lou12de39r/ashiyu/docs/stand_5deg.png

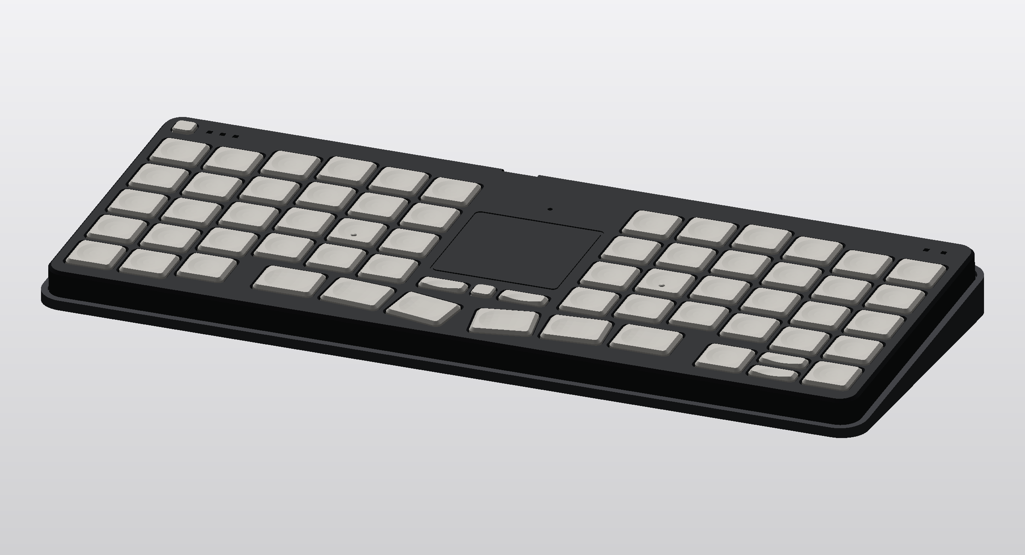
docs/stand_5deg.png
