lou12de39r/ashiyu/docs/case_black_top.png

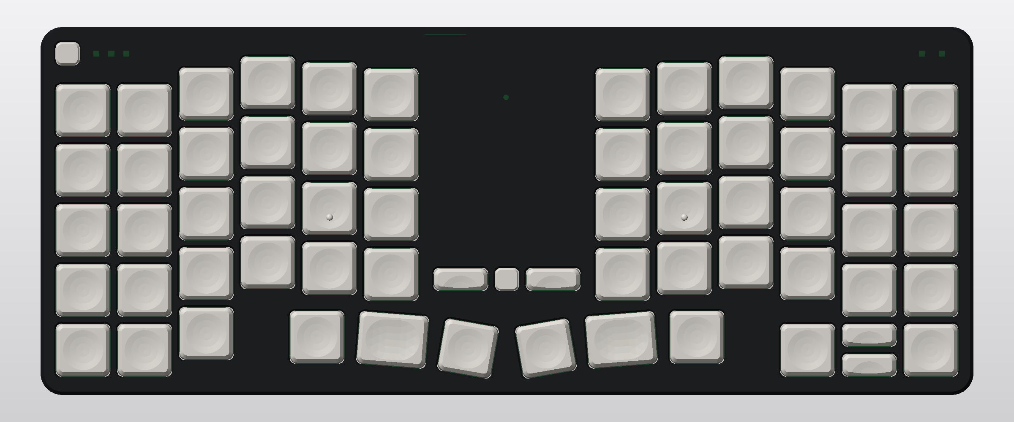
docs/case_black_top.png
