lou12de39r/ashiyu/docs/case_black_white_caps.png

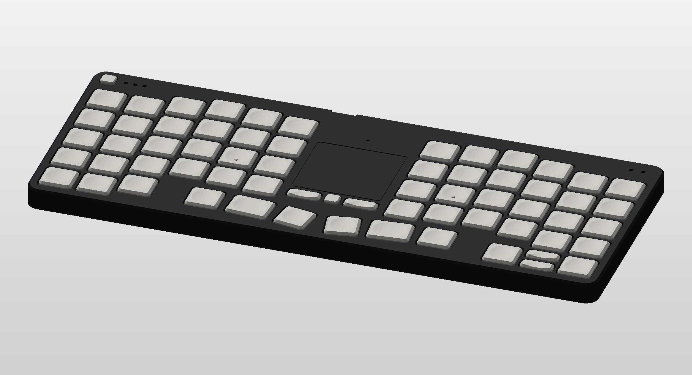
docs/case_black_white_caps.png
