lou12de39r/ashiyu/docs/case_bottom_plate.png

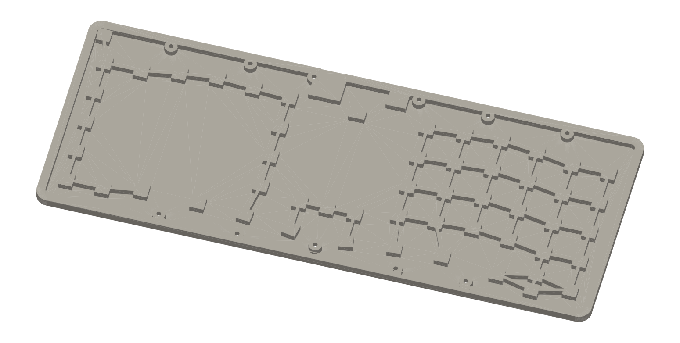
docs/case_bottom_plate.png
