lou12de39r/ashiyu/docs/case_keyhole_corners.png

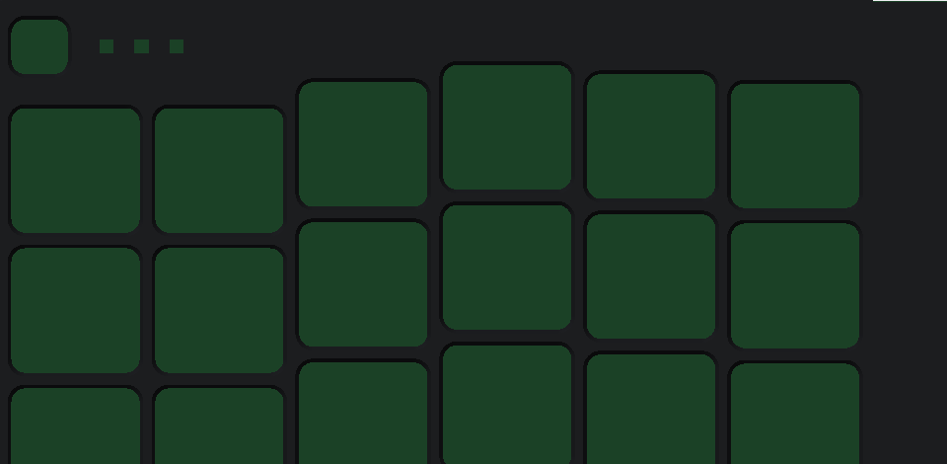
docs/case_keyhole_corners.png
