lou12de39r/ashiyu/docs/case_section_G.png

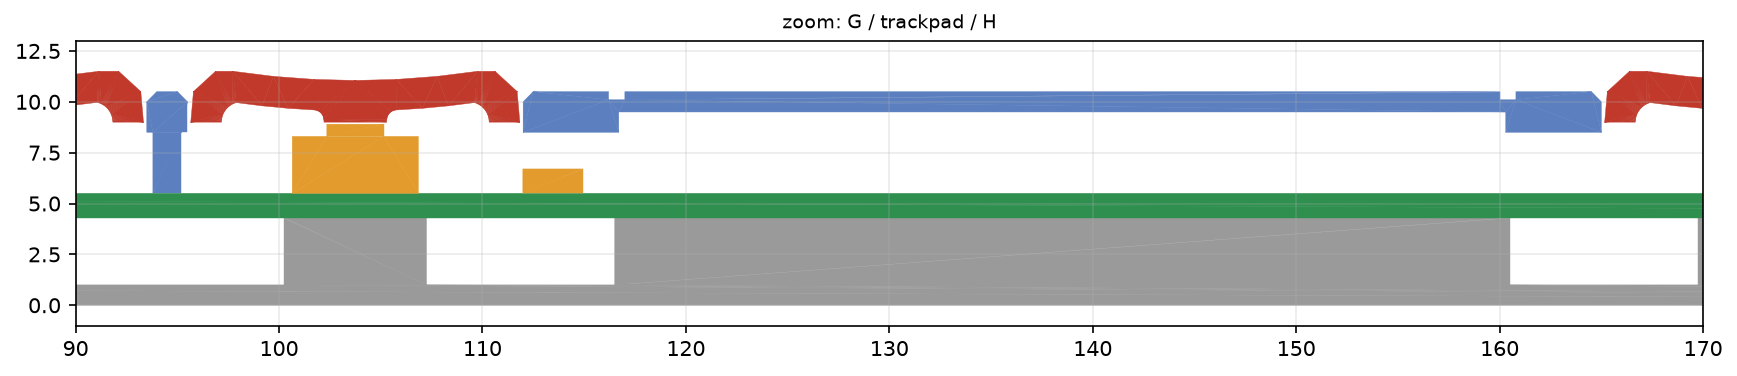
docs/case_section_G.png
