lou12de39r/ashiyu/docs/case_top.png

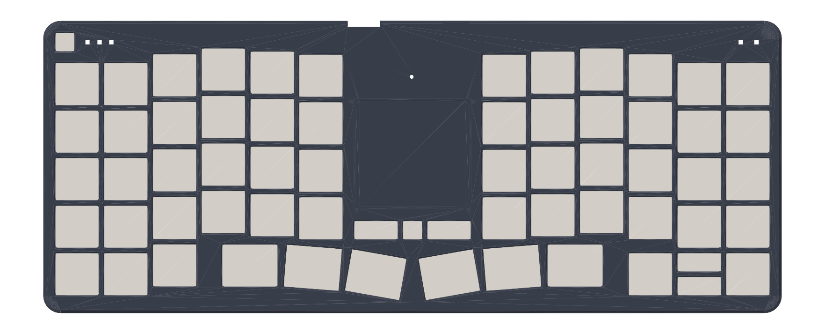
docs/case_top.png
