lou12de39r/ashiyu/docs/exterior_oblique.png

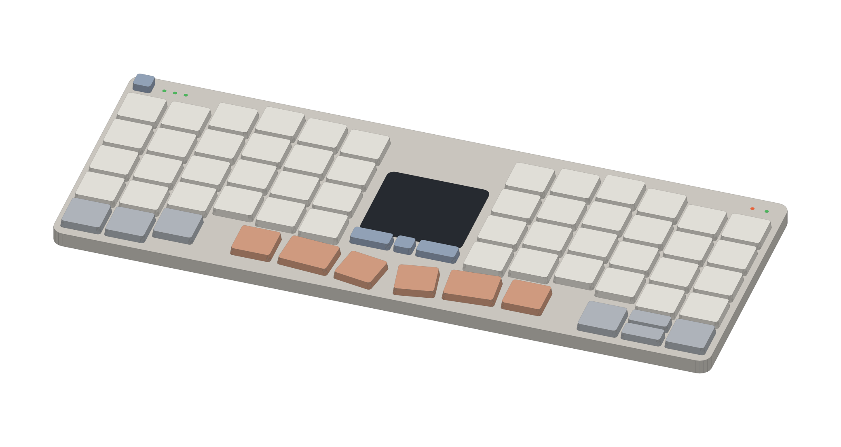
docs/exterior_oblique.png
