lou12de39r/ashiyu/docs/exterior_top.png

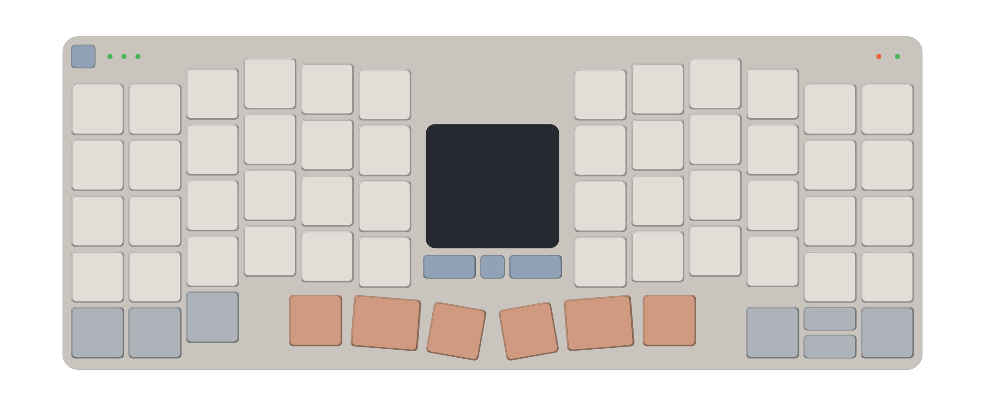
docs/exterior_top.png
