lou12de39r/ashiyu/docs/layout_splay6_compare.png

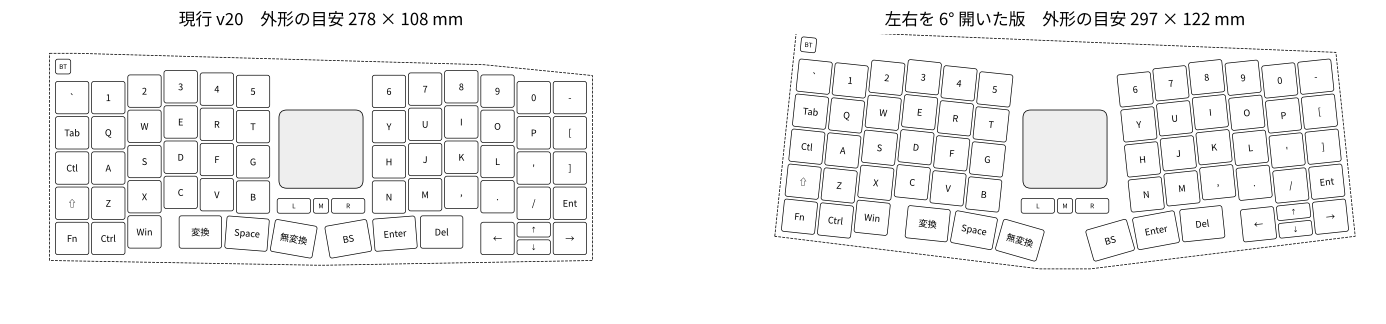
docs/layout_splay6_compare.png
