lou12de39r/ashiyu/docs/layout_stagger075_compare.png

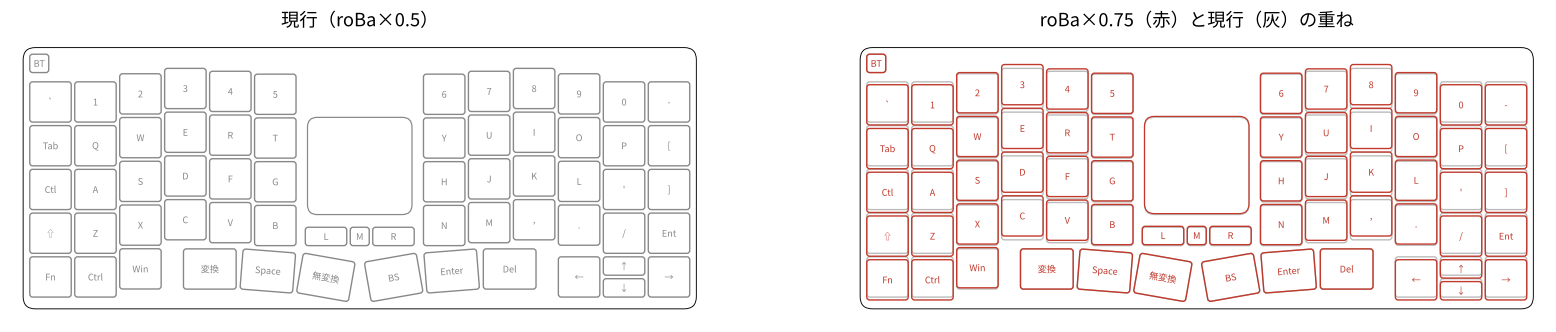
docs/layout_stagger075_compare.png
