lou12de39r/ashiyu/docs/pcb_3d_bottom.png

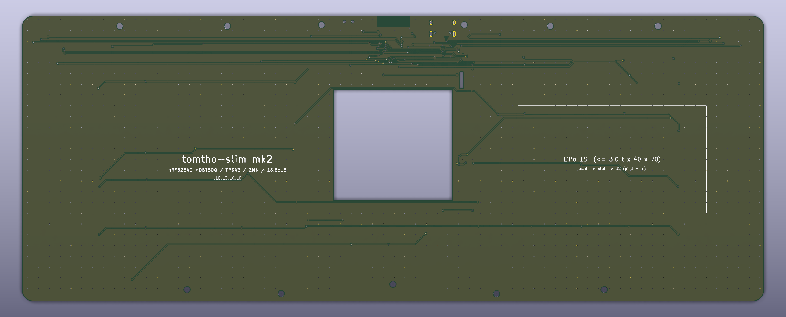
docs/pcb_3d_bottom.png
