lou12de39r/ashiyu/docs/pcb_3d_top.png

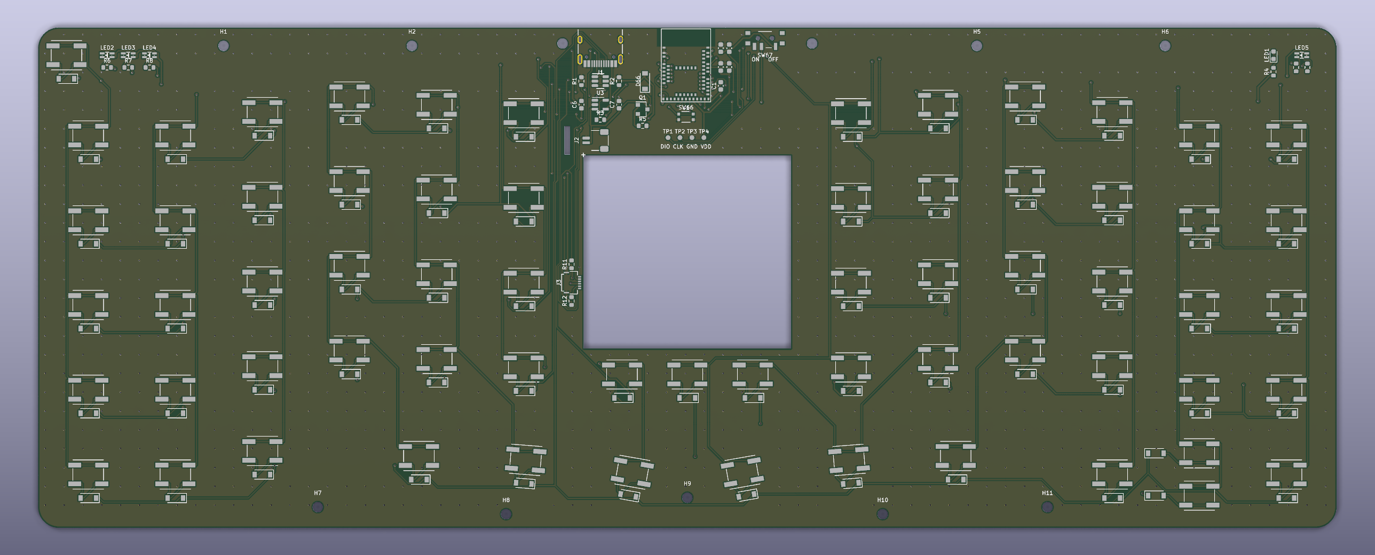
docs/pcb_3d_top.png
