lou12de39r/ashiyu/docs/pcb_center.png

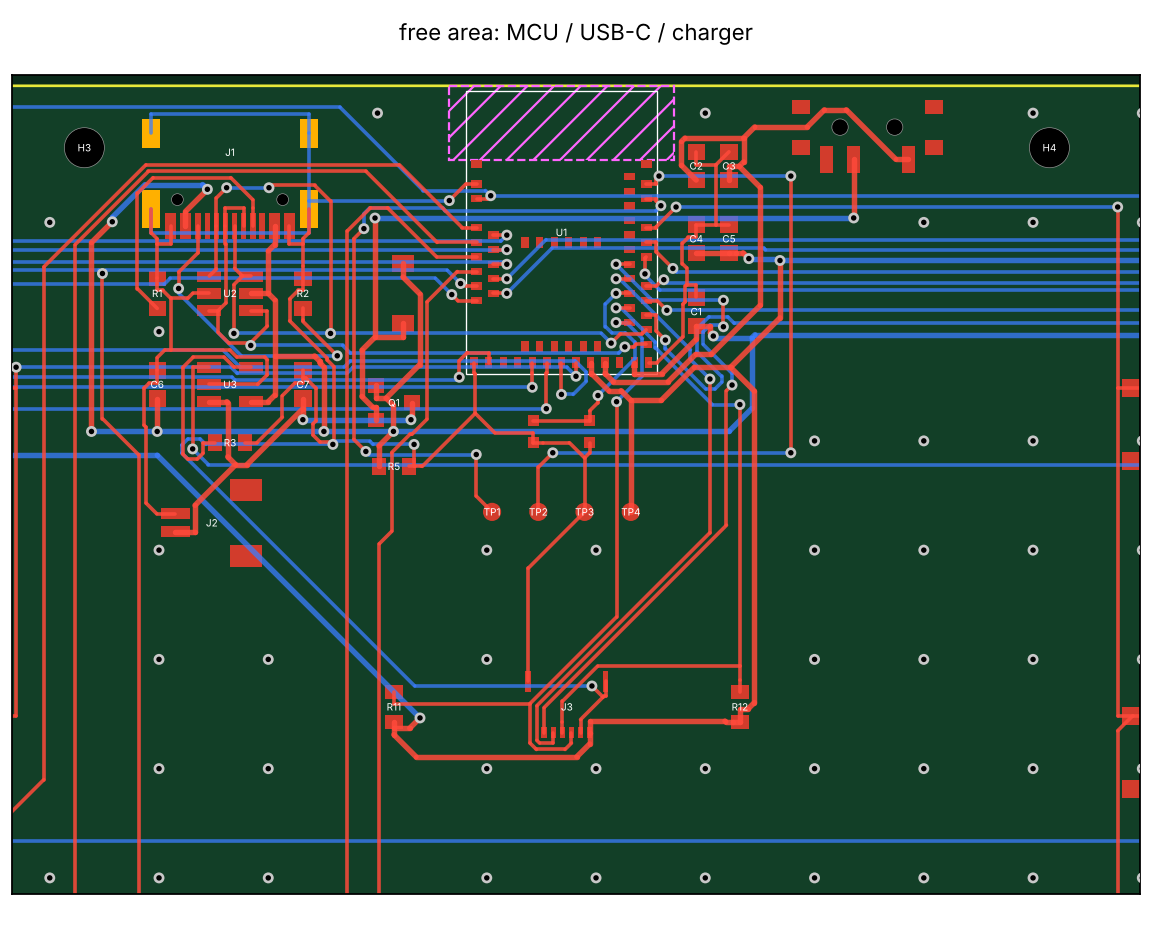
docs/pcb_center.png
