lou12de39r/ashiyu/docs/pcb_full.png

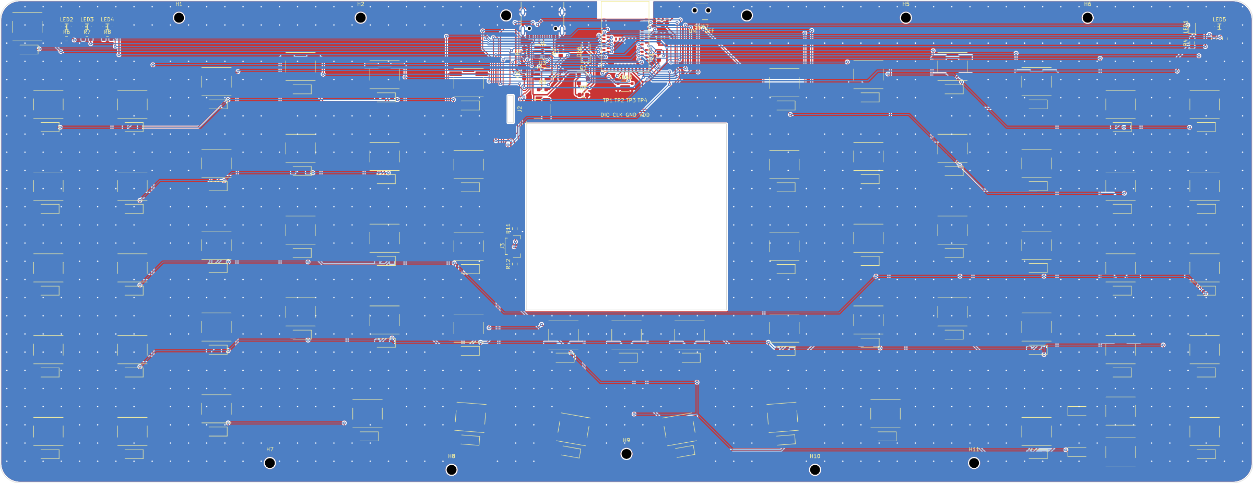
docs/pcb_full.png
