lou12de39r/ashiyu/docs/pcb_render_top.png

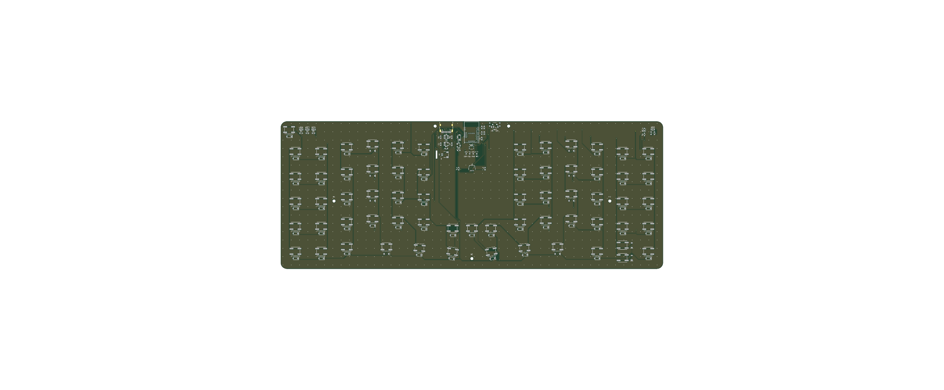
docs/pcb_render_top.png
