lou12de39r/ashiyu/docs/reset_plunger_section.png

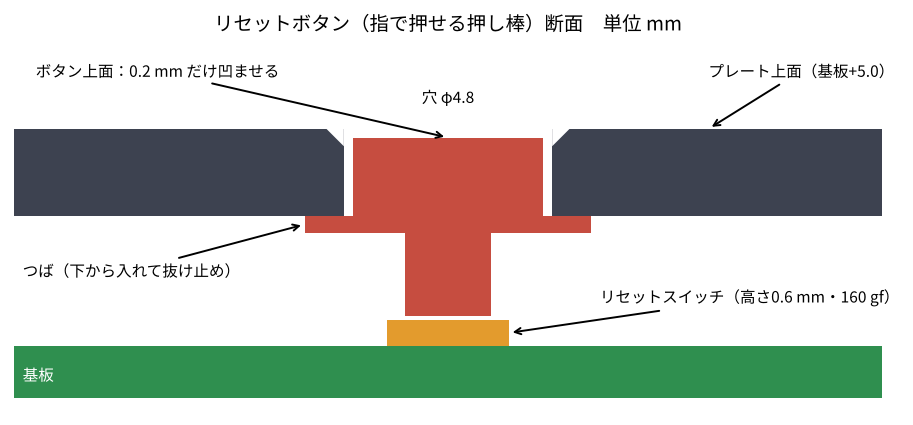
docs/reset_plunger_section.png
