lou12de39r/ashiyu/docs/stand_5deg_side.png

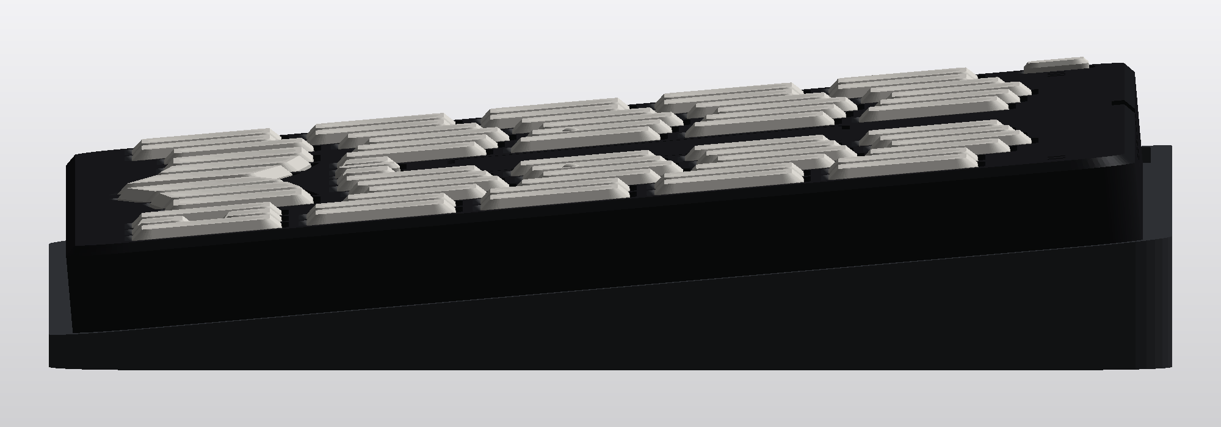
docs/stand_5deg_side.png
