lou12de39r/ashiyu/docs/thumb_1u_vs_125u.png

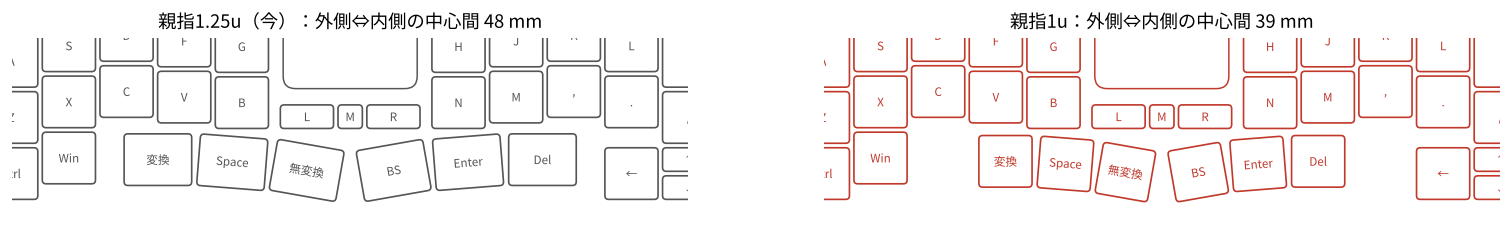
docs/thumb_1u_vs_125u.png
