lou12de39r/ashiyu/docs/trackpad_bottom.png

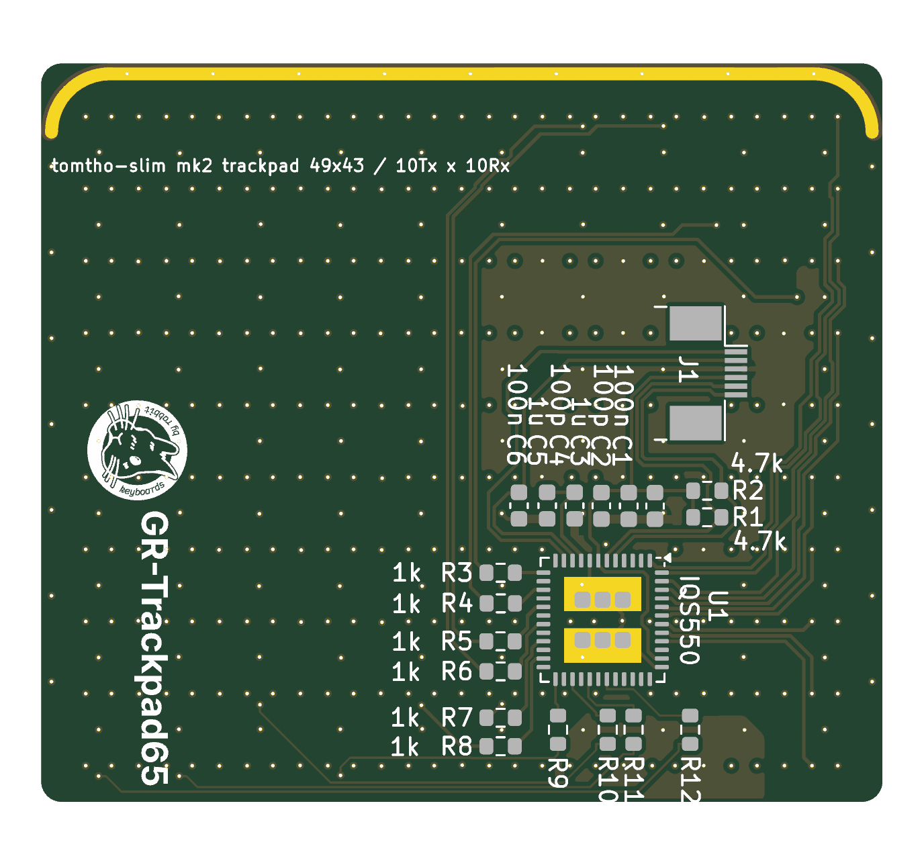
docs/trackpad_bottom.png
