lou12de39r/ashiyu/docs/trackpad_top.png

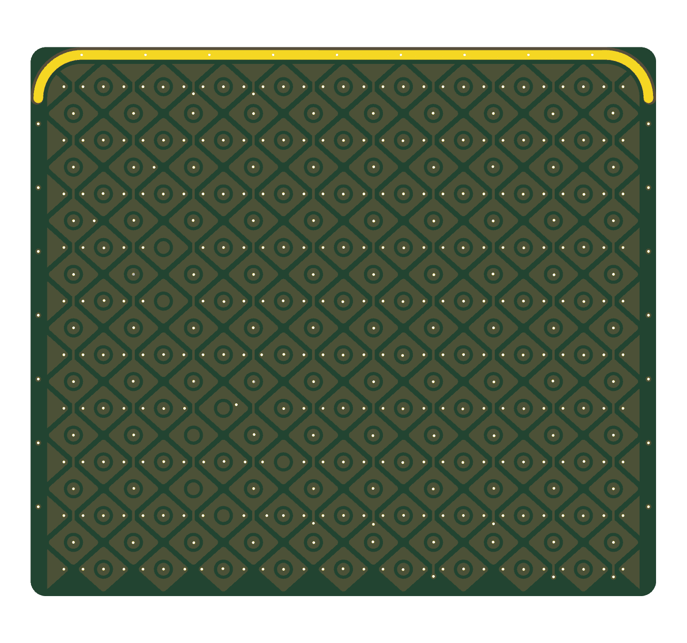
docs/trackpad_top.png
