lou12de39r/ashiyu/roba_ortho_v19.png

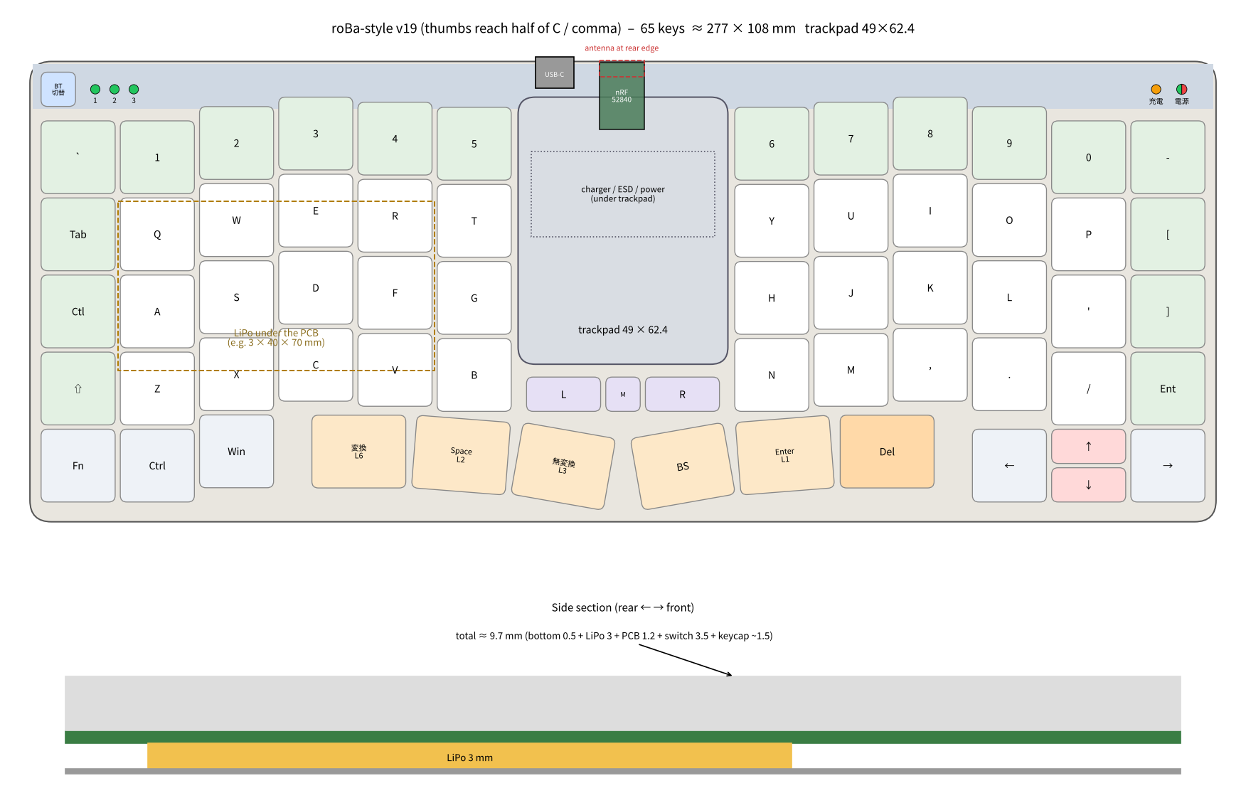
roba_ortho_v19.png
