lou12de39r/ashiyu/trackpad/work/bcu2.png

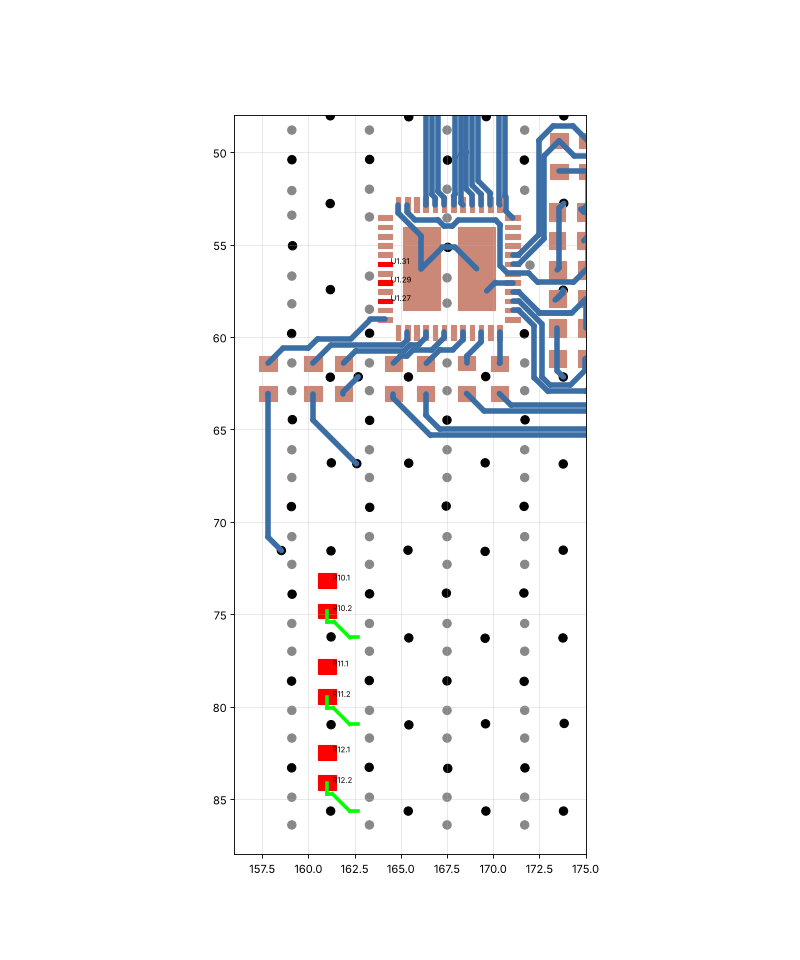
trackpad/work/bcu2.png
