lou12de39r/ashiyu/trackpad/work/bcu.png

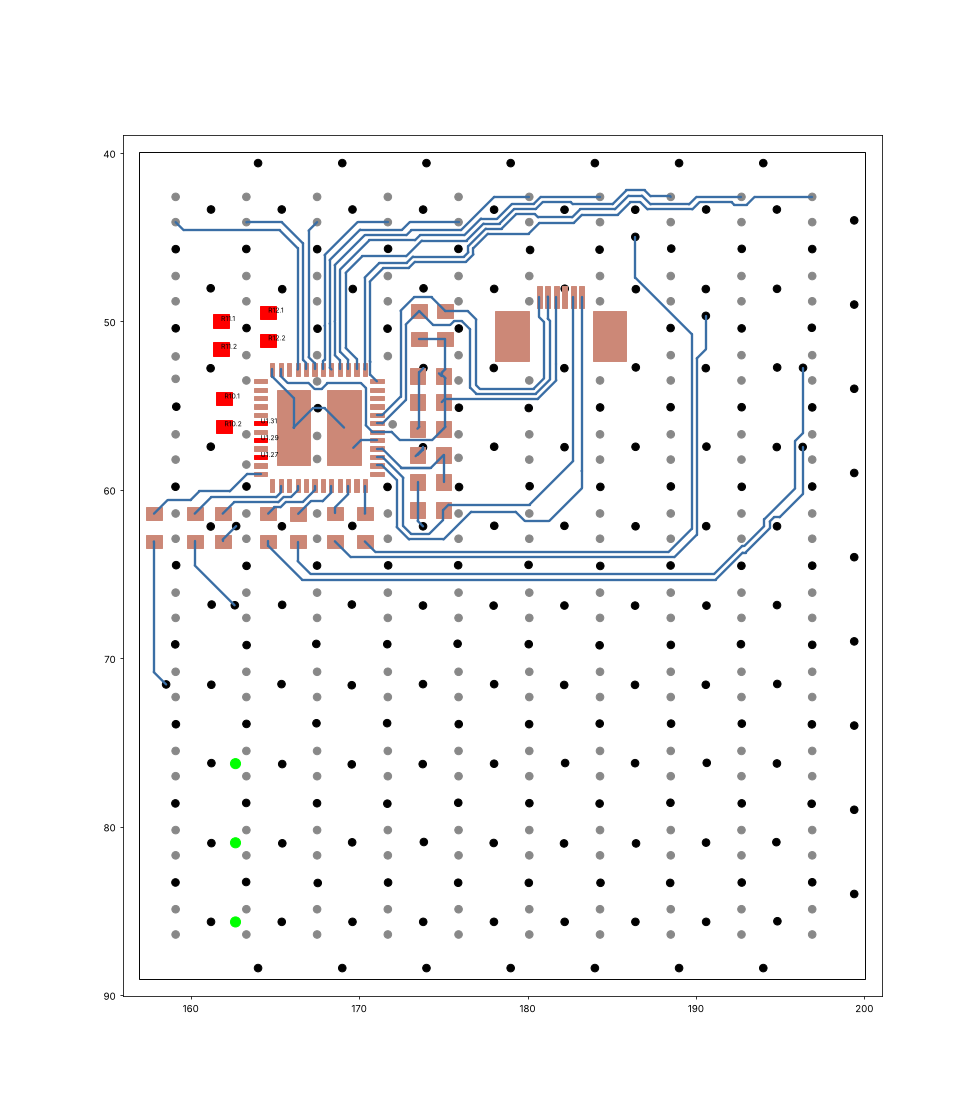
trackpad/work/bcu.png
