lou12de39r/ashiyu/layout_v20_print_A4.png

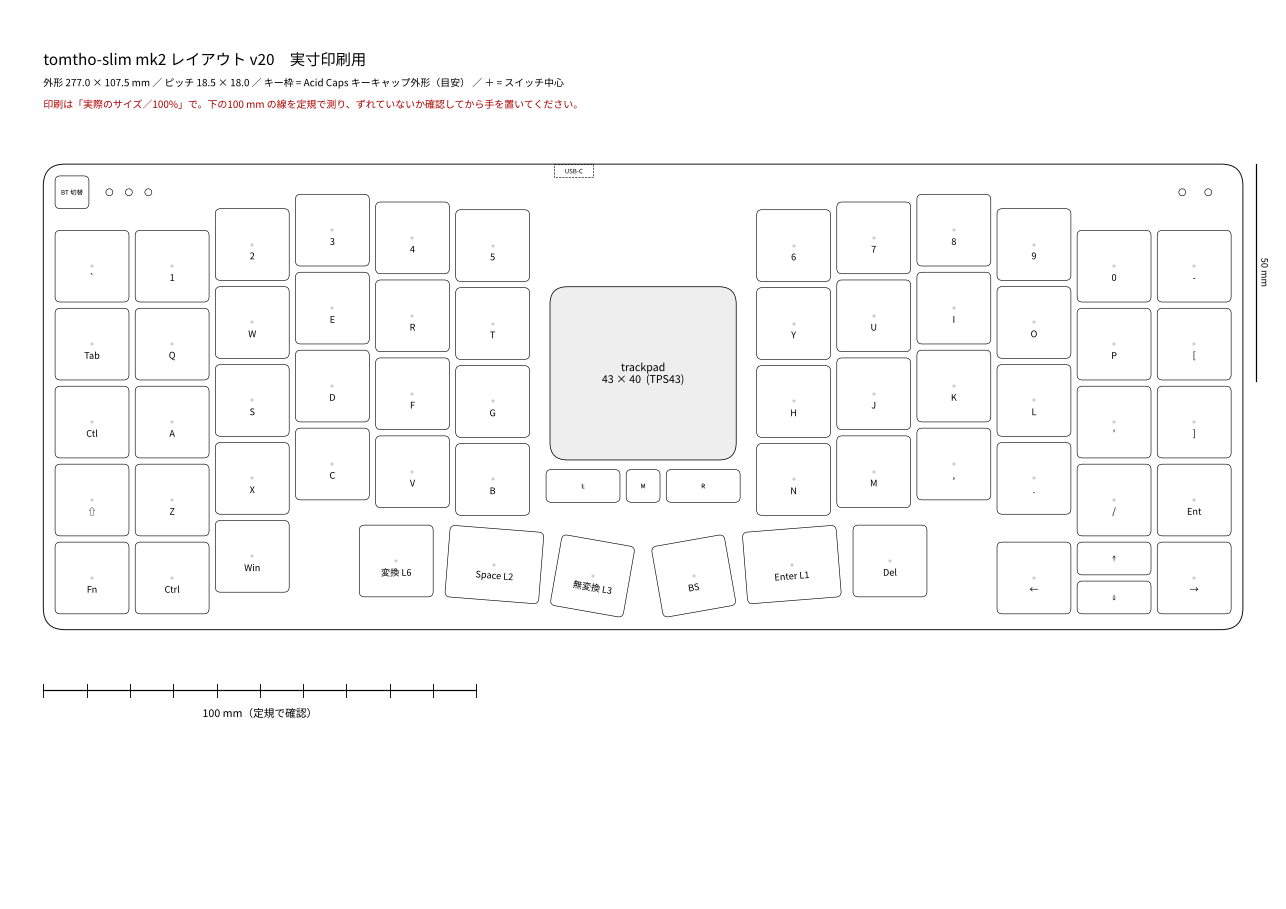
layout_v20_print_A4.png
